pctn0007/Motus/BuildInstImages/MOTUSSide.JPG

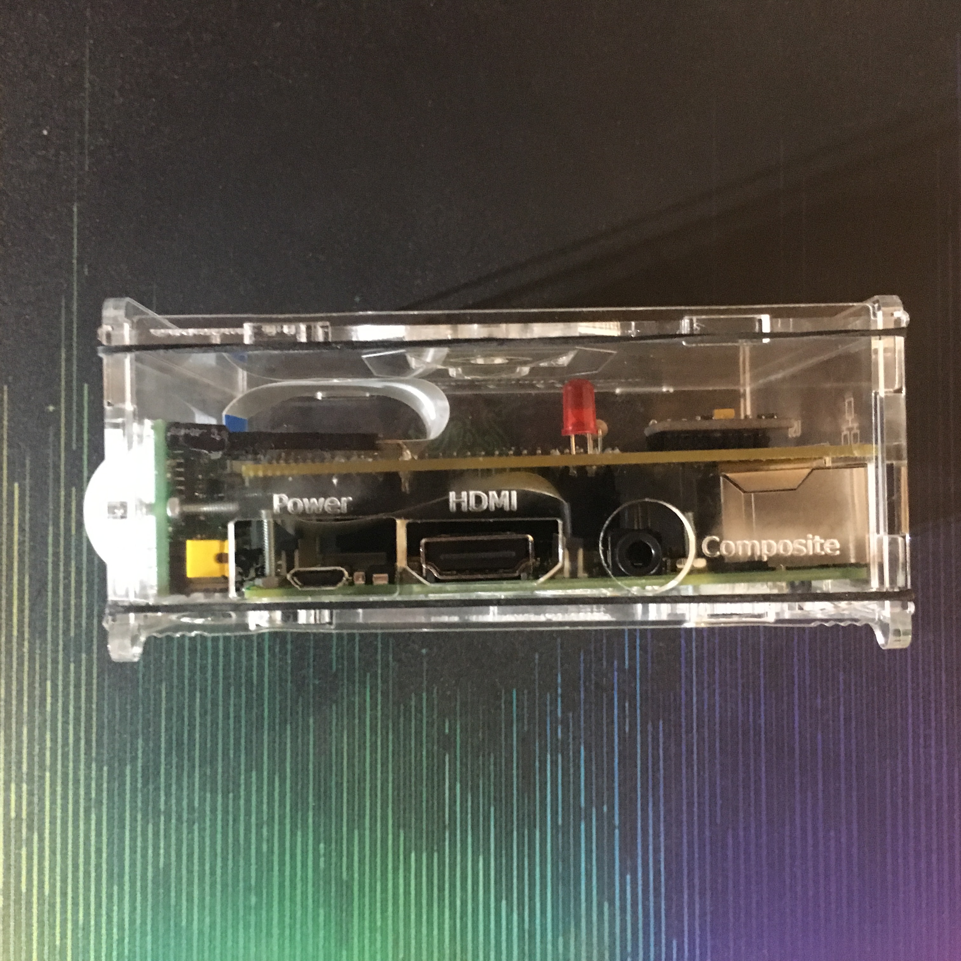
BuildInstImages/MOTUSSide.JPG
