pctn0007/Motus/Hardware_Code/test_scripts/LED.py

import RPi.GPIO as GPIO
import time
GPIO.setmode(GPIO.BCM)
GPIO.setwarnings(False)
GPIO.setup(17,GPIO.OUT)
GPIO.setup(4,GPIO.IN)
GPIO.output(17,GPIO.LOW)

while True:
        
        motion = GPIO.input(4)
        
        if motion is 1:
            GPIO.output(17,GPIO.HIGH)
            time.sleep(0.1)
            GPIO.output(17,GPIO.LOW)
            time.sleep(0.1)
