pctn0007/Motus/Hardware_Code/test_scripts/test1.py

# Import gcloud
from google.cloud import storage
import os
# location of json file created
credential_path = "c:\motus.json"
os.environ['GOOGLE_APPLICATION_CREDENTIALS'] = credential_path
# Enable Storage
client = storage.Client()

# Reference an existing bucket.
bucket = client.get_bucket('motus-e3989.appspot.com')

#image has to be the same location as python script
# Upload a local file to a new file to be created in your bucket.
zebraBlob = bucket.blob('zebra.jpg')
zebraBlob.upload_from_filename(filename='zebra.jpg')


# Download a file from your bucket.
#giraffeBlob = bucket.get_blob('zebra.jpg')
#giraffeBlob.download_as_string()
#In line client = storage.Client()
