pctn0007/Motus/Hardware_Code/test_scripts/firebaseConnection.py

import random
from firebase import firebase

firebase = firebase.FirebaseApplication('https://motus-e3989.firebaseio.com/', None)

result = firebase.post('/random',{'ID':random.randrange(100000, 999999, 6)})

print(result)
